FlyGlas/WMRP/layout/wmrp_place_smd.png

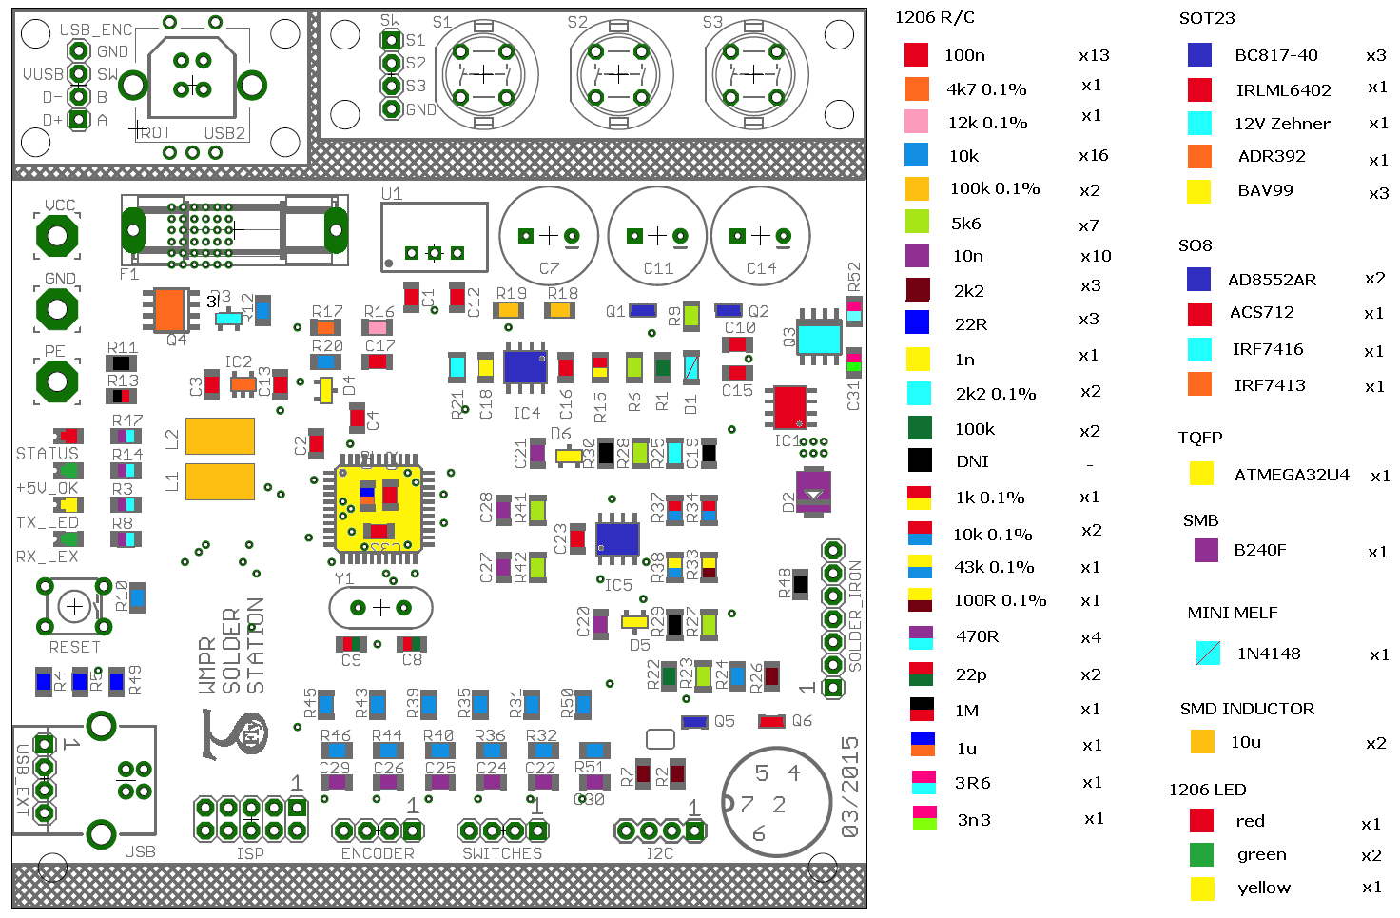
layout/wmrp_place_smd.png
