FlyGlas/WMRP/pictures/IMG_20150321_175302.jpg

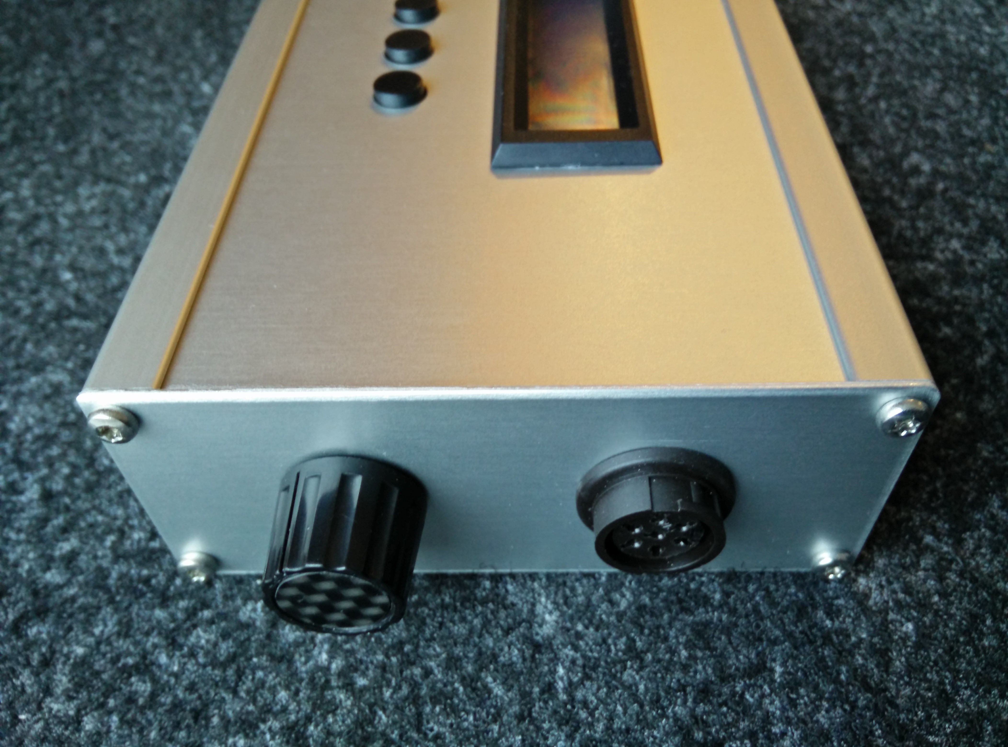
pictures/IMG_20150321_175302.jpg
