FlyGlas/WMRP/pictures/IMG_20150321_175408.jpg

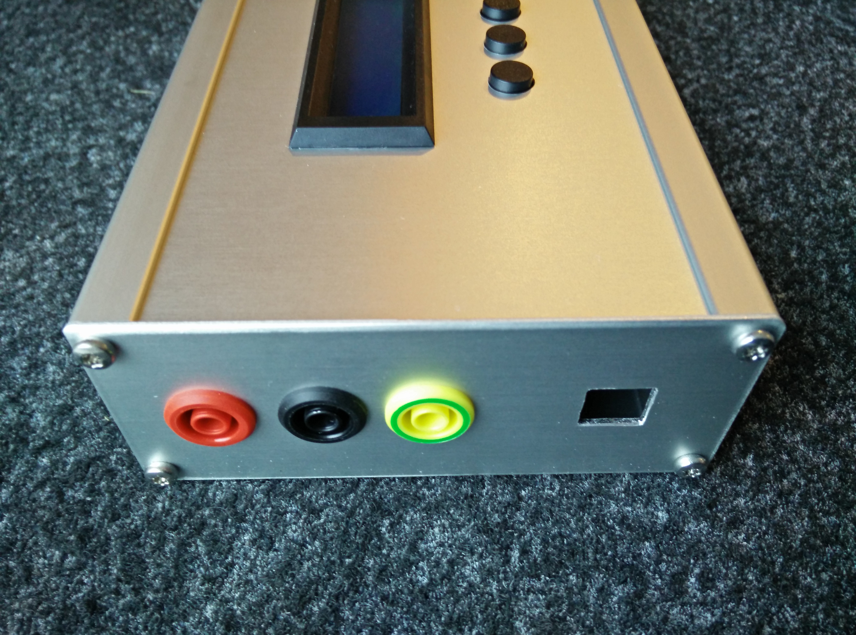
pictures/IMG_20150321_175408.jpg
