FlyGlas/WMRP/pictures/IMG_20150321_175450.jpg

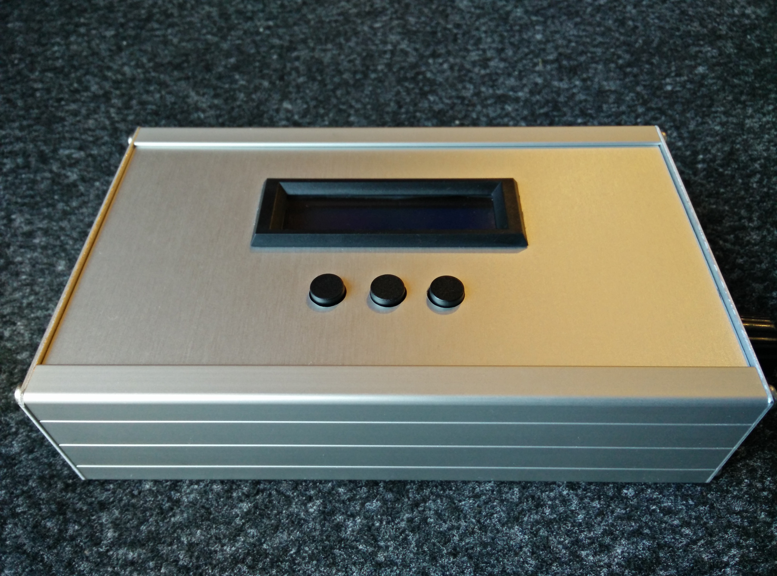
pictures/IMG_20150321_175450.jpg
