FlyGlas/WMRP/pictures/IMG_20150418_105648.JPG

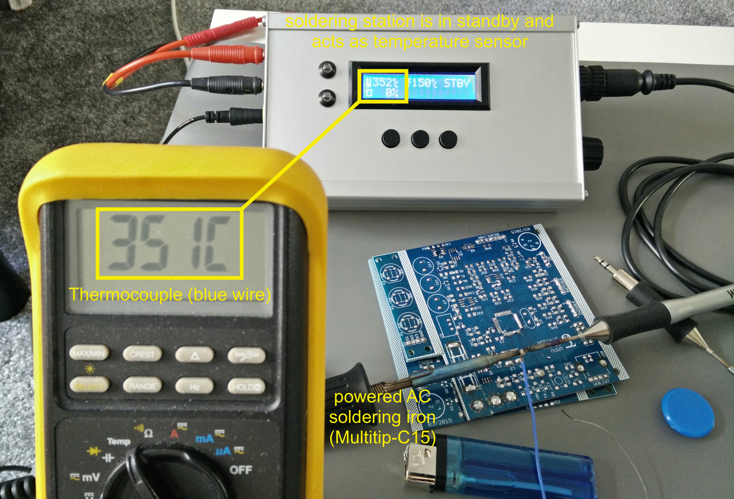
pictures/IMG_20150418_105648.JPG
