FlyGlas/WMRP/pictures/pin_assignment_wmrp_de.png

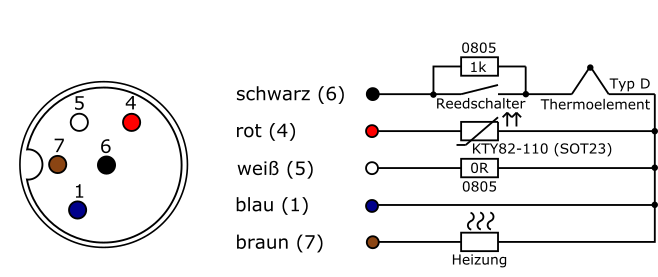
pictures/pin_assignment_wmrp_de.png
